phil31/BOX-Miner/images/First_proto/First_Proto_16xBM1366 B 3D.jpg

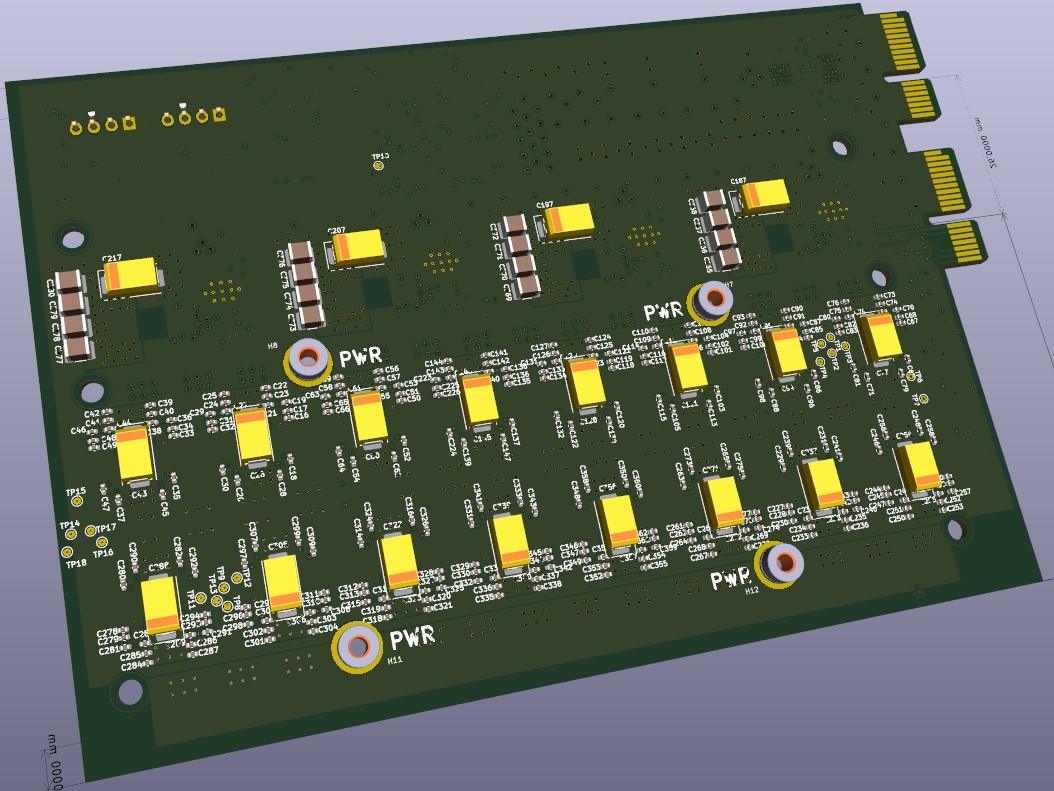
images/First_proto/First_Proto_16xBM1366 B 3D.jpg
