phil31/BOX-Miner/EKO_Miner_ASIClib.sch/TMP1075NDRLR.step

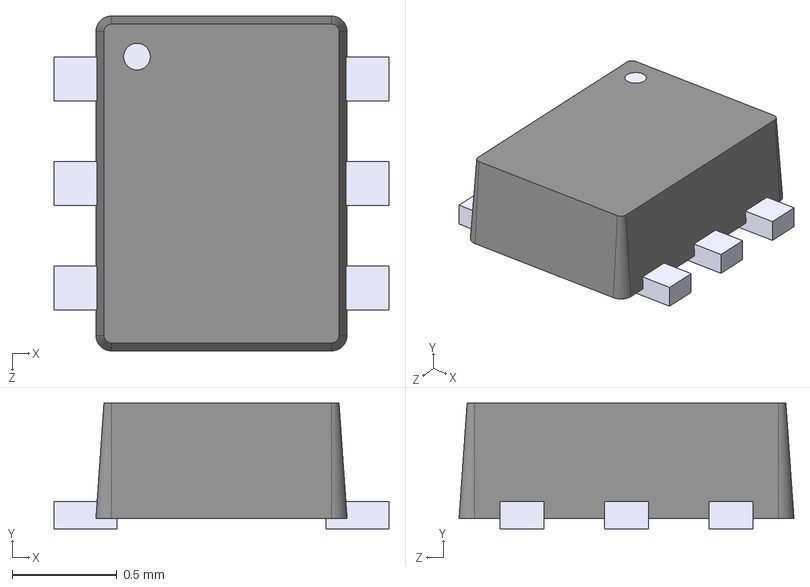
[picture p30: CAD file, 2024-12-08]
EKO_Miner_ASIClib.sch/TMP1075NDRLR.step
1.60 x 0.6 x 1.60 mm
