phil31/BOX-Miner/3D/EKO_Miner Box AsicBoard/EKO_Miner_AsicBoard-16xBM1368-01A.step

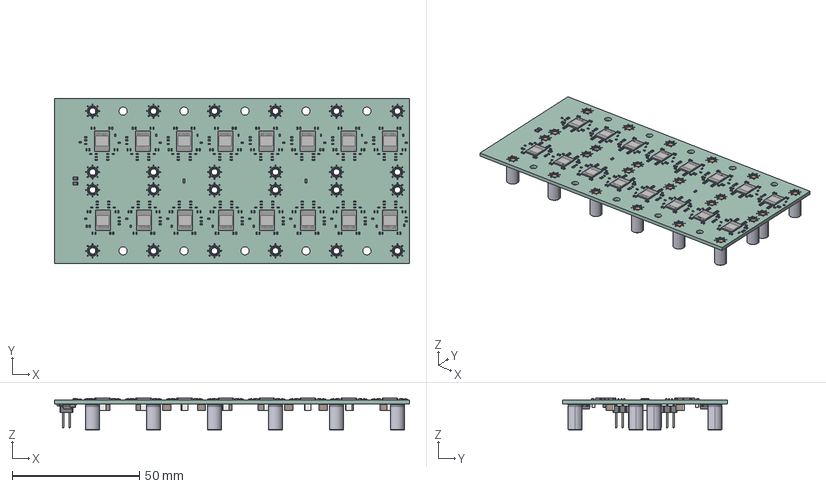
[picture p31: CAD file, 2024-12-11]
3D/EKO_Miner Box AsicBoard/EKO_Miner_AsicBoard-16xBM1368-01A.step
139.8 x 65.0 x 12.4 mm
C_0402_1005Metric x 256
R_0402_1005Metric x 82
BM1368PB x 16
R_0603_1608Metric x 2
R_0805_2012Metric x 2
C_0805_2012Metric x 5
C_1210_3225Metric x 26
PinHeader_2x04_P254mm_Vertical_SMD x 2
MIC39100-3.3WS-TR x 2
AsicsBoard - 16xBM1368 - 01A_PCB
