phil31/BOX-Miner/3D/EKO_Miner Box enclosure 3 lanes v1/Support PCB BM13xx-16 01a.SLDPRT

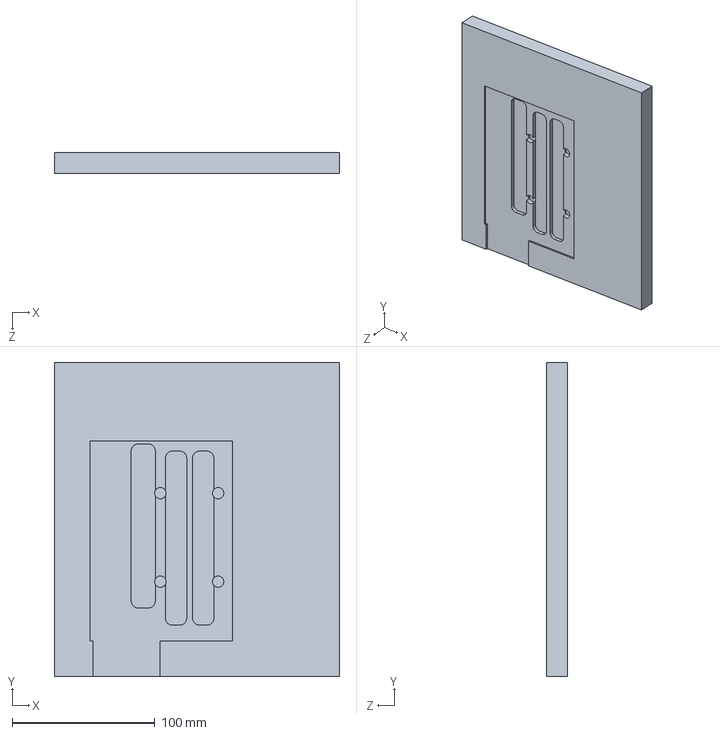
[picture p32: CAD file, 2024-12-08]
3D/EKO_Miner Box enclosure 3 lanes v1/Support PCB BM13xx-16 01a.SLDPRT
200.0 x 220.0 x 15.0 mm
