phil31/BOX-Miner/3D/EKO_Miner build 10xBM1370 V1.00.3MF

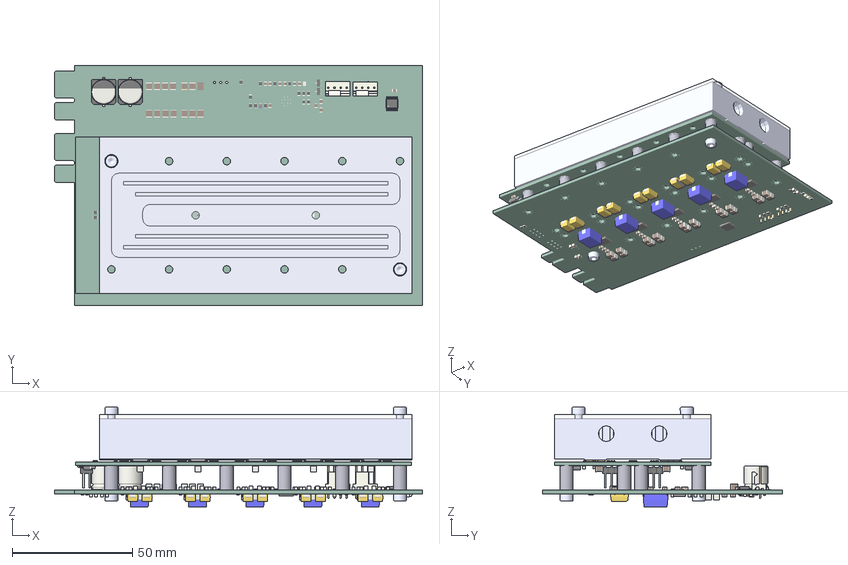
[picture p33: CAD file, 2024-12-08]
3D/EKO_Miner build 10xBM1370 V1.00.3MF
153.0 x 99.8 x 41.4 mm
