phil31/BOX-Miner/3D/EKO_Miner Box AsicBoard/EKO_Miner_AsicBoard-BM13xx Heatsink Base 02A.SLDPRT

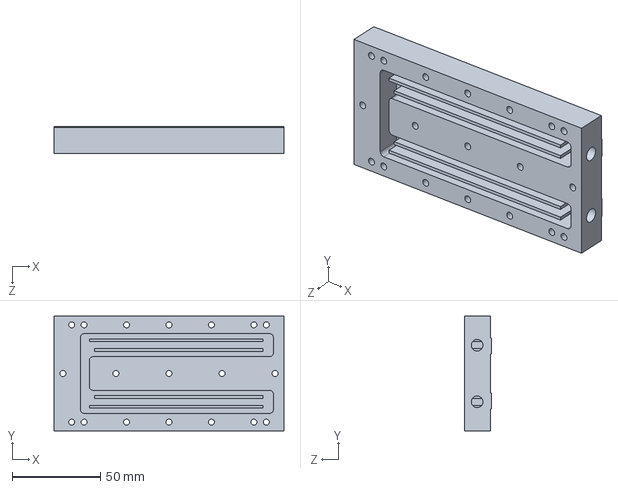
[picture p34: CAD file, 2024-12-11]
3D/EKO_Miner Box AsicBoard/EKO_Miner_AsicBoard-BM13xx Heatsink Base 02A.SLDPRT
130.0 x 65.0 x 15.0 mm
