phil31/BOX-Miner/3D/EKO_Miner WaterBlock V1.0/EKO_Miner WaterBlock V1.0 A.SLDPRT

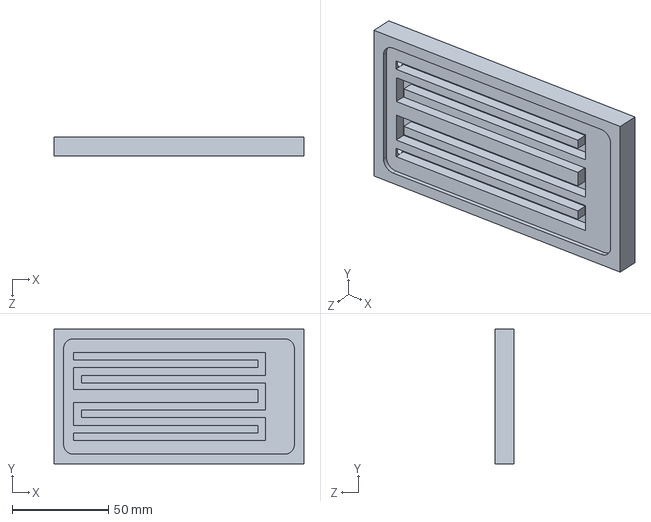
[picture p35: CAD file, 2024-12-08]
3D/EKO_Miner WaterBlock V1.0/EKO_Miner WaterBlock V1.0 A.SLDPRT
130.0 x 70.0 x 10.0 mm
