phil31/BOX-Miner/3D/EKO_Miner Box AsicBoard/EKO_Miner_AsicBoard-10xBM1370-01A.step

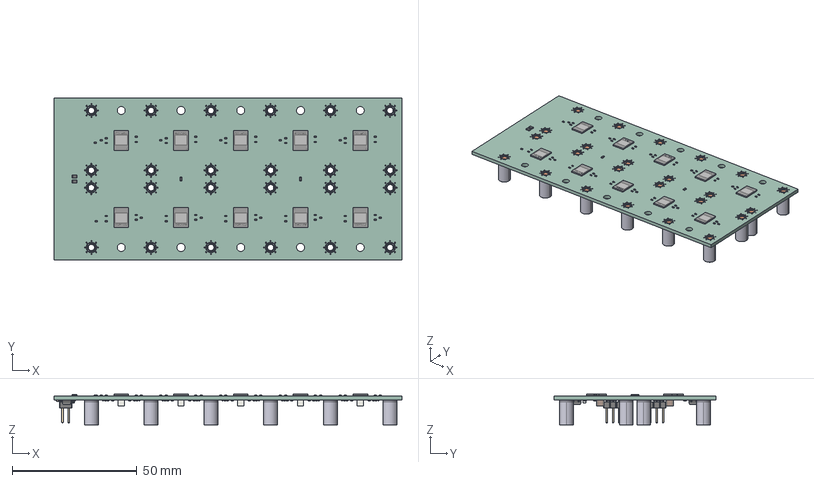
[picture p36: CAD file, 2024-12-11]
3D/EKO_Miner Box AsicBoard/EKO_Miner_AsicBoard-10xBM1370-01A.step
139.8 x 65.0 x 12.4 mm
R_0402_1005Metric x 52
BM1368PB x 10
R_0805_2012Metric x 2
R_0603_1608Metric x 2
C_0402_1005Metric x 163
C_1210_3225Metric x 10
PinHeader_2x04_P254mm_Vertical_SMD x 2
C_0805_2012Metric x 2
MIC39100-3.3WS-TR x 2
ASEMB
AsicsBoard - 10xBM1370 - 01A_PCB
