phil31/BOX-Miner/3D/EKO_Miner Box enclosure 3 lanes v1/exports/EKO_Miner_BM1366 BM13xx-16 01A HEATSINK - single ASIC.STEP

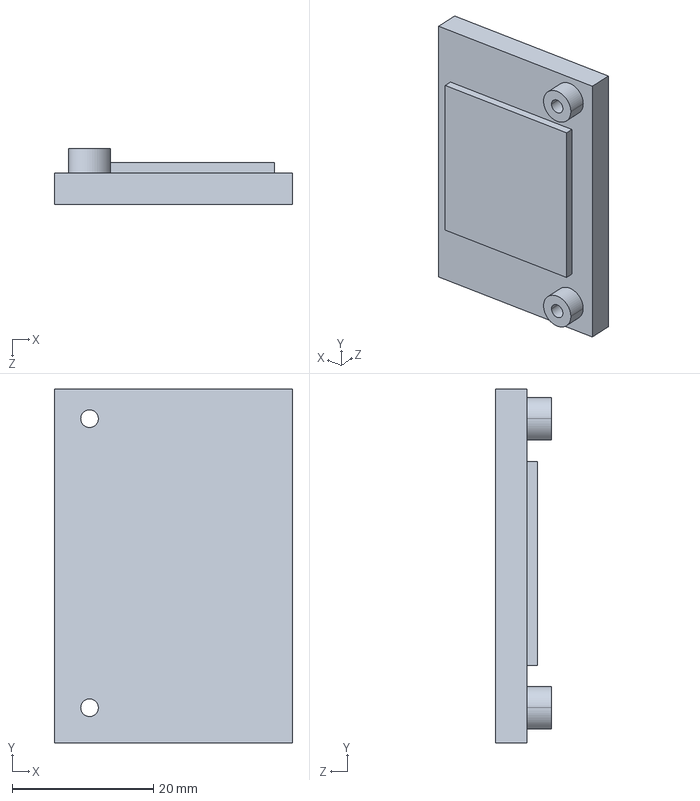
[picture p37: CAD file, 2024-12-08]
3D/EKO_Miner Box enclosure 3 lanes v1/exports/EKO_Miner_BM1366 BM13xx-16 01A HEATSINK - single ASIC.STEP
33.8 x 50.2 x 8.00 mm
