phil31/BOX-Miner/3D/EKO_Miner Box enclosure 3 lanes v1/exports/BarBus 40.5mm.STEP

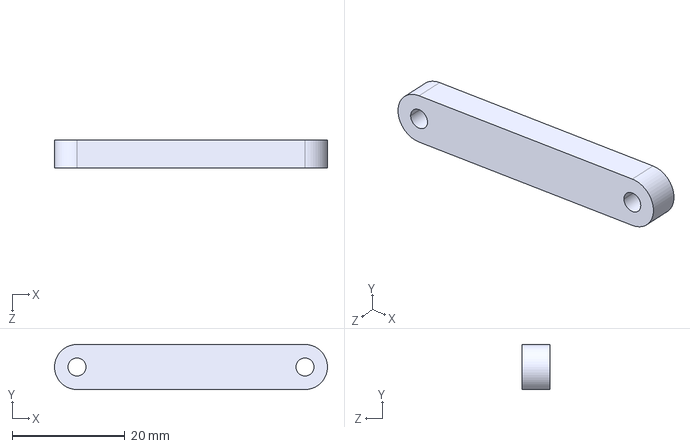
[picture p40: CAD file, 2024-12-08]
3D/EKO_Miner Box enclosure 3 lanes v1/exports/BarBus 40.5mm.STEP
48.5 x 8.00 x 5.00 mm
