phil31/BOX-Miner/3D/EKO_Miner WaterBlock V1.0/EKO_Miner WaterBlock V1.0 Couvercle.SLDPRT

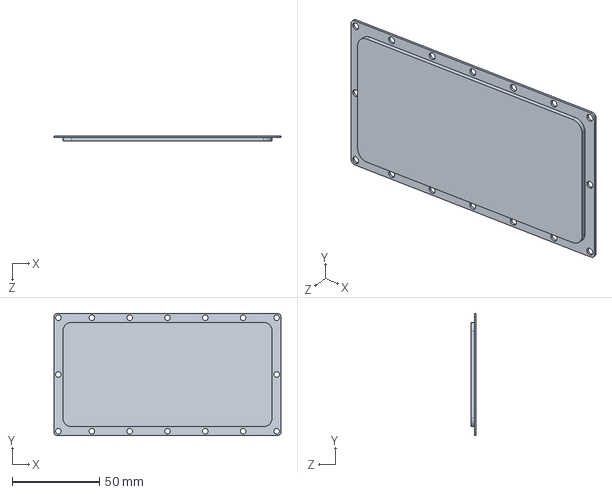
[picture p41: CAD file, 2024-12-08]
3D/EKO_Miner WaterBlock V1.0/EKO_Miner WaterBlock V1.0 Couvercle.SLDPRT
130.0 x 70.0 x 3.00 mm
