phil31/BOX-Miner/3D/EKO_Miner Box enclosure 3 lanes v1/ick_s_98_x_98_x_30.SLDPRT

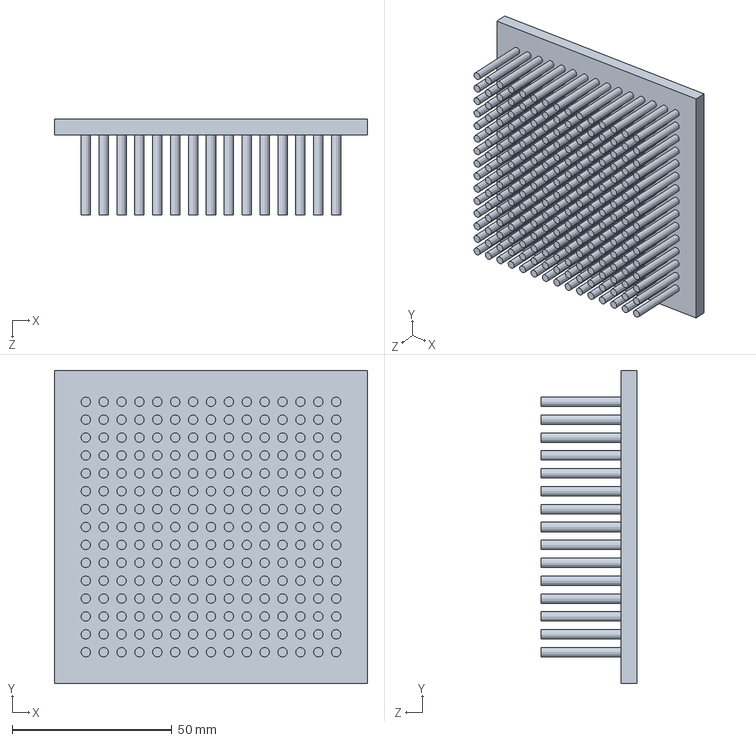
[picture p42: CAD file, 2024-12-08]
3D/EKO_Miner Box enclosure 3 lanes v1/ick_s_98_x_98_x_30.SLDPRT
98.0 x 98.0 x 30.0 mm
