phil31/BOX-Miner/3D/EKO_Miner Box AsicBoard/EKO_Miner_AsicBoard-16xBM13xx-01A Heatsink.SLDPRT

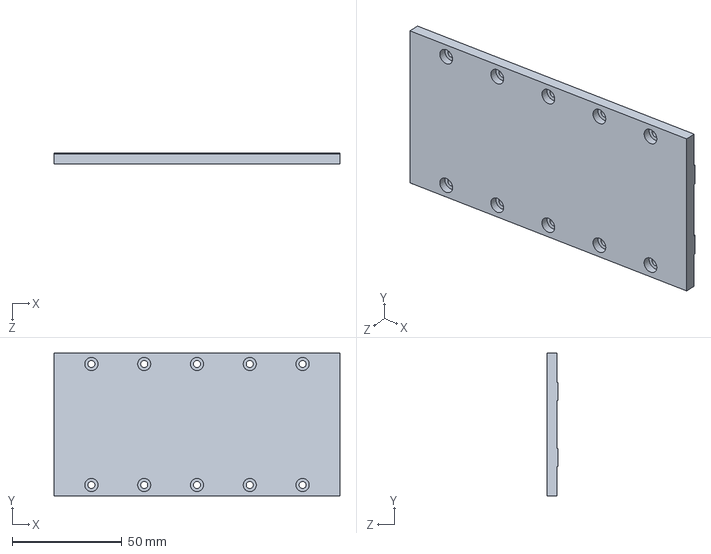
[picture p43: CAD file, 2024-12-08]
3D/EKO_Miner Box AsicBoard/EKO_Miner_AsicBoard-16xBM13xx-01A Heatsink.SLDPRT
130.0 x 65.0 x 5.00 mm
