phil31/BOX-Miner/3D/EKO_Miner Box enclosure 3 lanes v1/EKO_Miner_BM1366 PCBonly.step

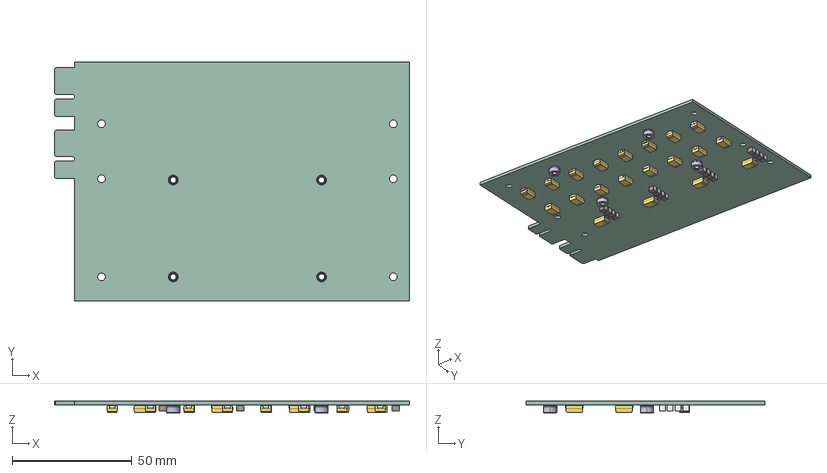
[picture p44: CAD file, 2024-12-08]
3D/EKO_Miner Box enclosure 3 lanes v1/EKO_Miner_BM1366 PCBonly.step
148.4 x 99.8 x 4.88 mm
CP_EIA_7343_31_Kemet_D x 20
C_1210_3225Metric x 16
EKO_Miner_BM1366-13xx_16-01A PCBonly_PCB
