phil31/BOX-Miner/3D/EKO_Miner Box enclosure 3 lanes v1/exports/EKO_Miner_BM1366 BM13xx-16 01A HEATSINK.STEP

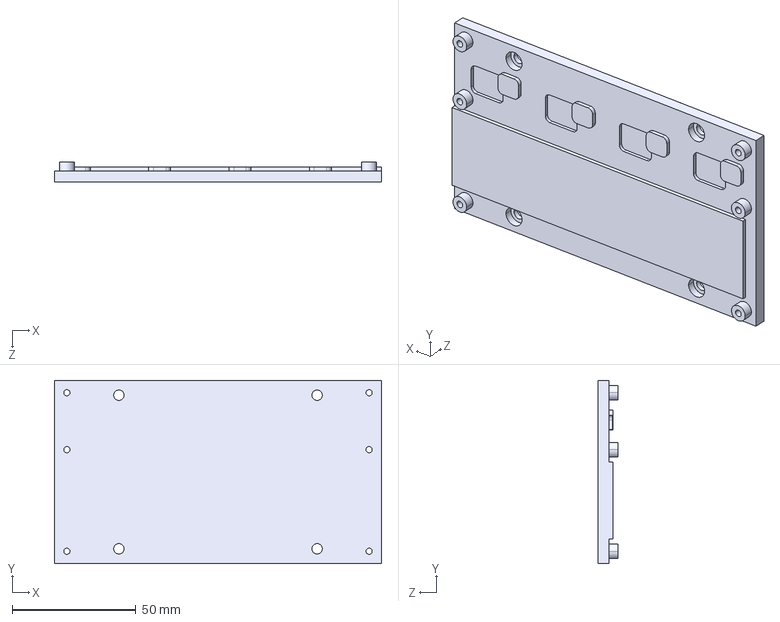
[picture p45: CAD file, 2024-12-08]
3D/EKO_Miner Box enclosure 3 lanes v1/exports/EKO_Miner_BM1366 BM13xx-16 01A HEATSINK.STEP
132.0 x 74.0 x 8.00 mm
