phil31/BOX-Miner/3D/EKO_Miner Box AsicBoard/EKO_Miner_AsicBoard-Template-01A.step

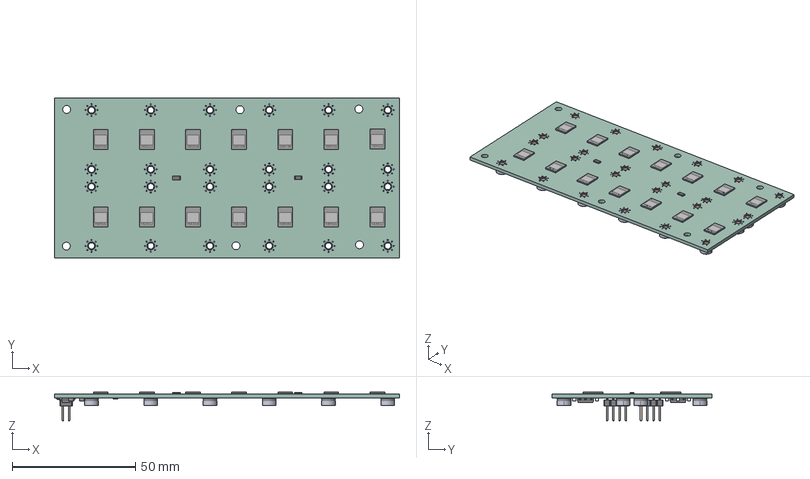
[picture p47: CAD file, 2024-12-08]
3D/EKO_Miner Box AsicBoard/EKO_Miner_AsicBoard-Template-01A.step
139.8 x 65.0 x 11.7 mm
BM1368PB x 14
R_1206_3216Metric x 2
C_0805_2012Metric x 5
PinHeader_2x04_P254mm_Vertical_SMD x 2
MIC39100-3.3WS-TR x 2
R_0805_2012Metric x 2
EKO_Miner_AsicsBoard_Template_01A_PCB
