phil31/BOX-Miner/3D/EKO_Miner Box AsicBoard/EKO_Miner_AsicBoard-BM13xx Heatsink Base 01A.SLDPRT

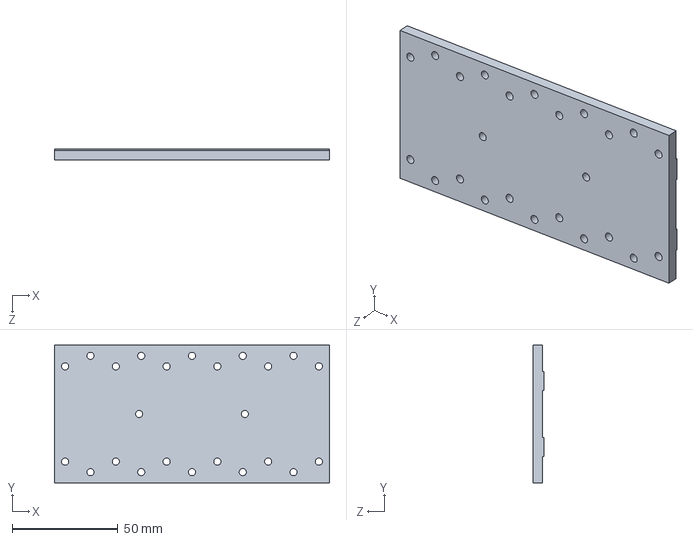
[picture p48: CAD file, 2024-12-08]
3D/EKO_Miner Box AsicBoard/EKO_Miner_AsicBoard-BM13xx Heatsink Base 01A.SLDPRT
130.0 x 65.0 x 5.00 mm
