phil31/BOX-Miner/images/Assembled_board_10xBM1370.jpg

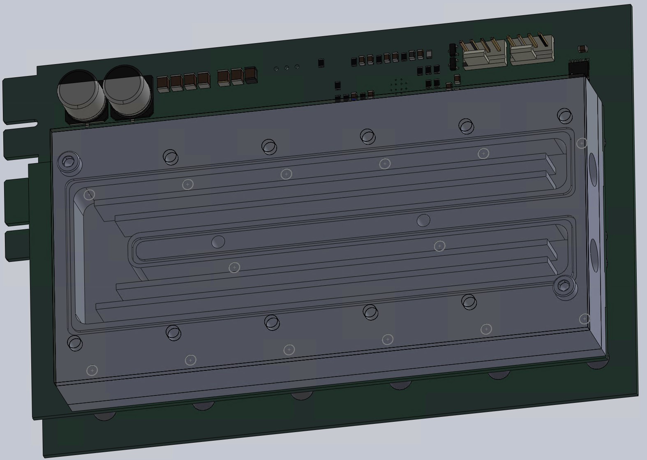
images/Assembled_board_10xBM1370.jpg
